Epaminondaslage/quadro_de_chamadas/img/quadro_de_chamadas4.jpeg

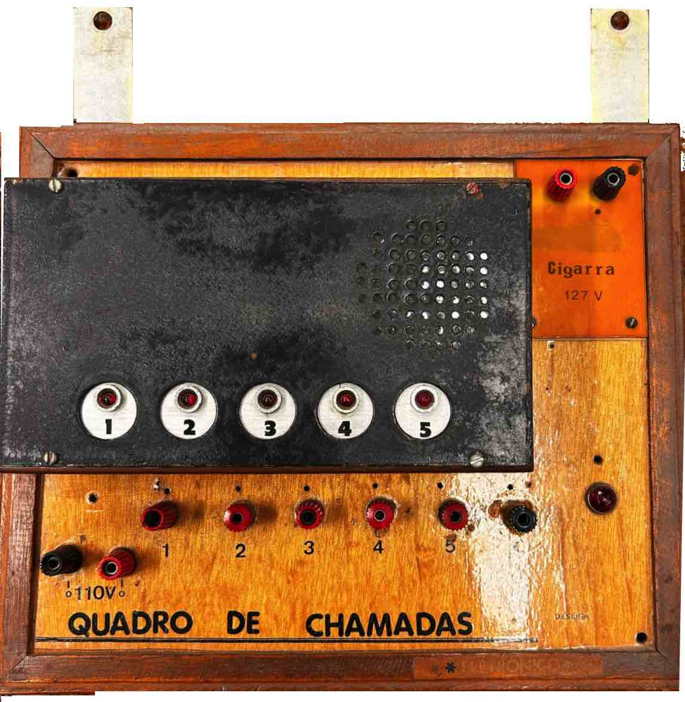
img/quadro_de_chamadas4.jpeg
